RehanShakoor/liner_motorized_stage/experiment_pic2.jpg

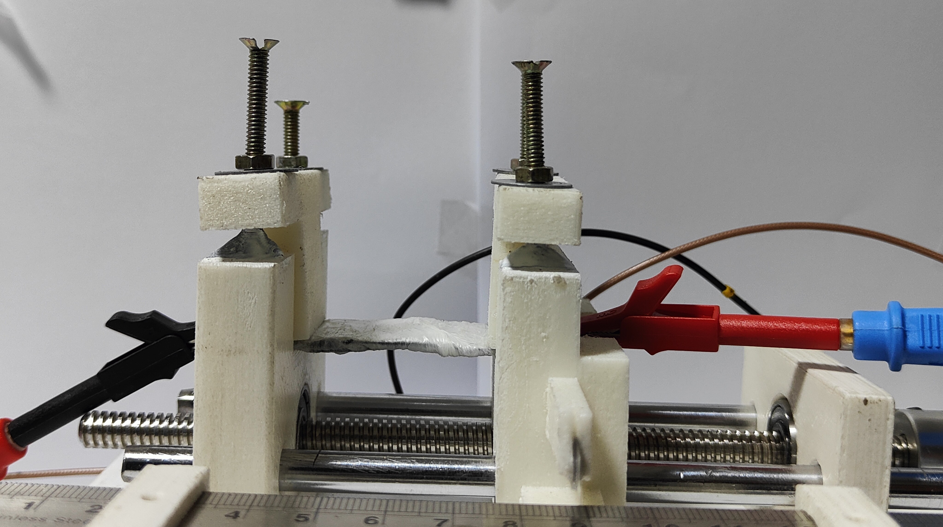
experiment_pic2.jpg
